NeerajR18/version1/Assets/Keycaps/Bottom_row1u.step

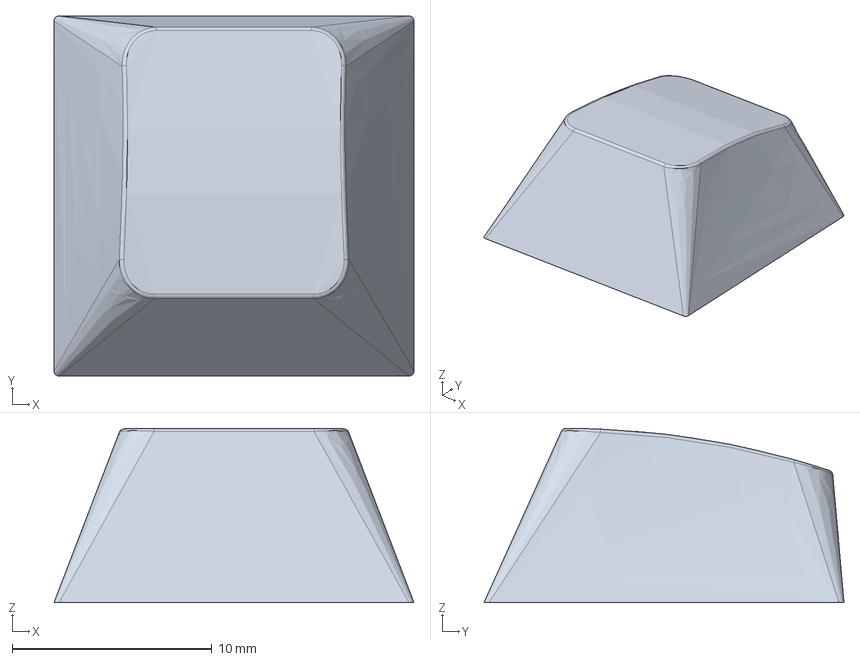
[picture p16: CAD file, 2026-05-22]
Assets/Keycaps/Bottom_row1u.step
18.0 x 18.0 x 8.70 mm
