NeerajR18/version1/Assets/Keycaps/Tab_key.step

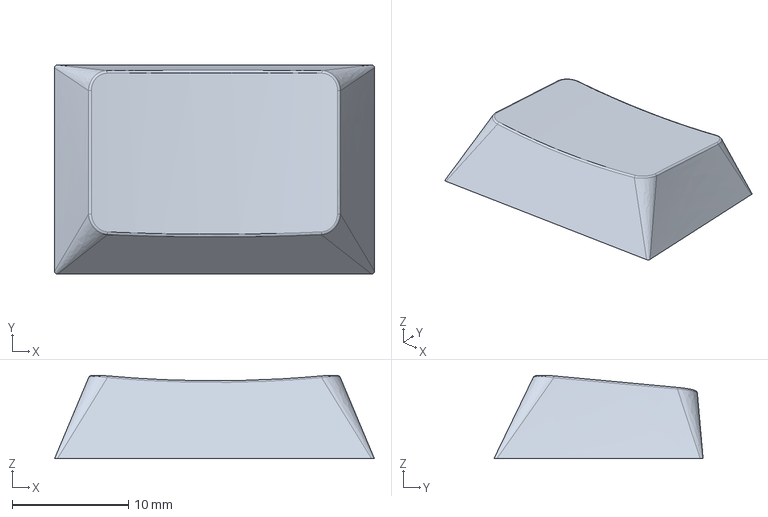
[picture p17: CAD file, 2026-05-22]
Assets/Keycaps/Tab_key.step
27.5 x 18.0 x 7.18 mm
