NeerajR18/version1/Assets/Keycaps/ESC_and_Function_keys.step

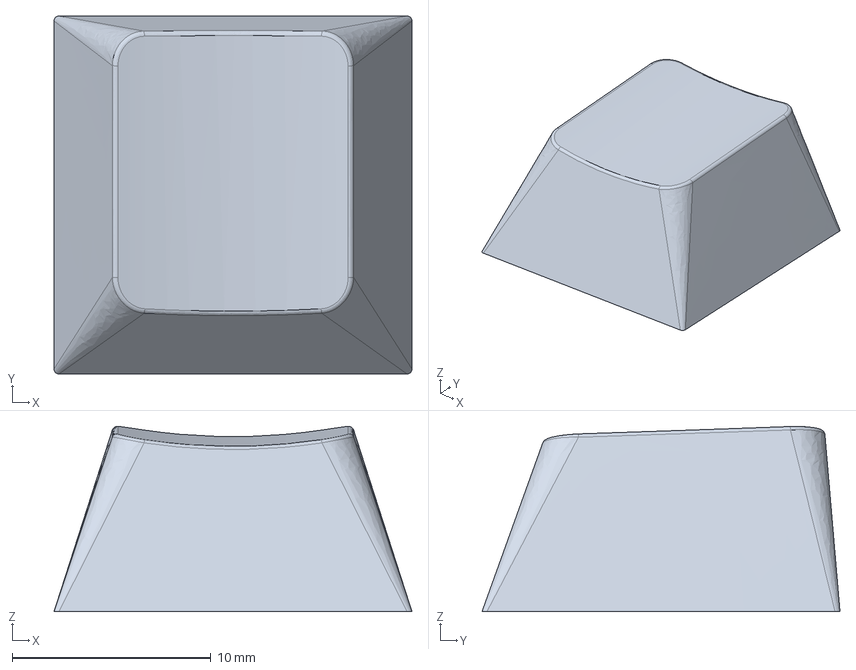
[picture p18: CAD file, 2026-05-22]
Assets/Keycaps/ESC_and_Function_keys.step
18.0 x 18.0 x 9.30 mm
