NeerajR18/version1/Assets/Keycaps/middle_row.step

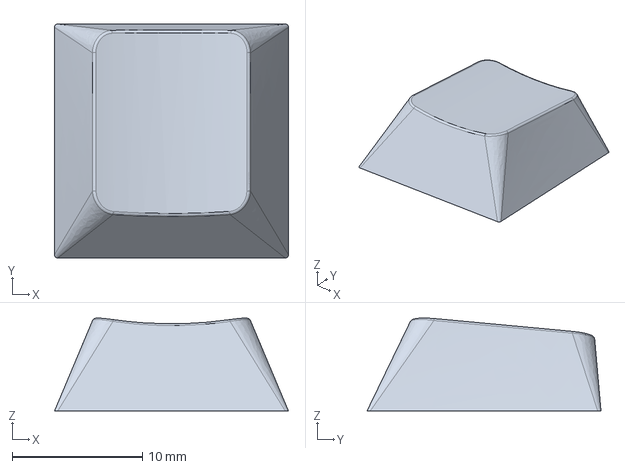
[picture p19: CAD file, 2026-05-22]
Assets/Keycaps/middle_row.step
18.0 x 18.0 x 7.15 mm
