NeerajR18/version1/Assets/Keycaps/Caps.step

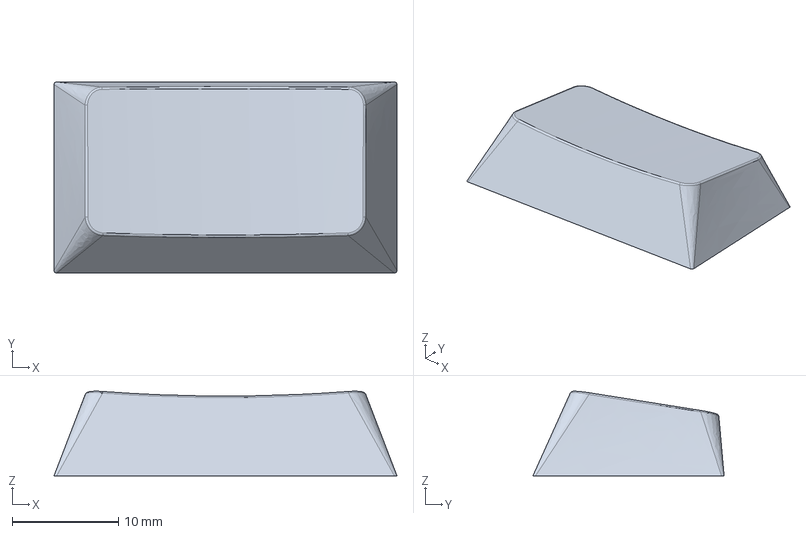
[picture p20: CAD file, 2026-05-22]
Assets/Keycaps/Caps.step
32.3 x 18.0 x 7.96 mm
