NeerajR18/version1/Assets/Keycaps/Back_sp.step

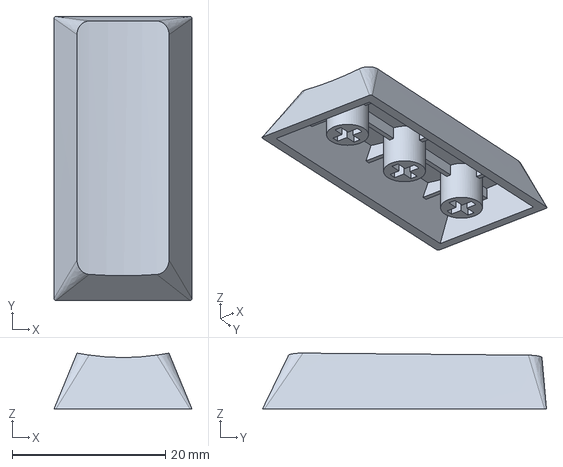
[picture p21: CAD file, 2026-05-22]
Assets/Keycaps/Back_sp.step
18.0 x 37.0 x 7.28 mm
