NeerajR18/version1/Assets/Keycaps/Space_bar.step

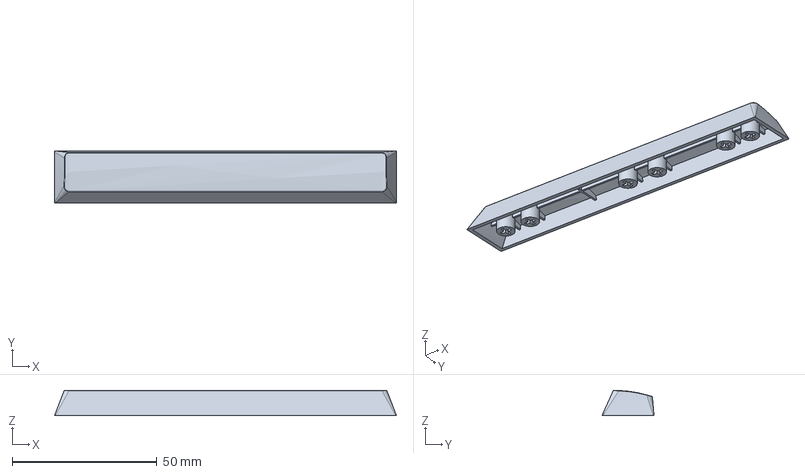
[picture p22: CAD file, 2026-05-22]
Assets/Keycaps/Space_bar.step
118.0 x 18.0 x 8.70 mm
